herraa1/msx-jio-cart-v1/images/msx-jiocart-v1-flashing-with-wrtsst.png

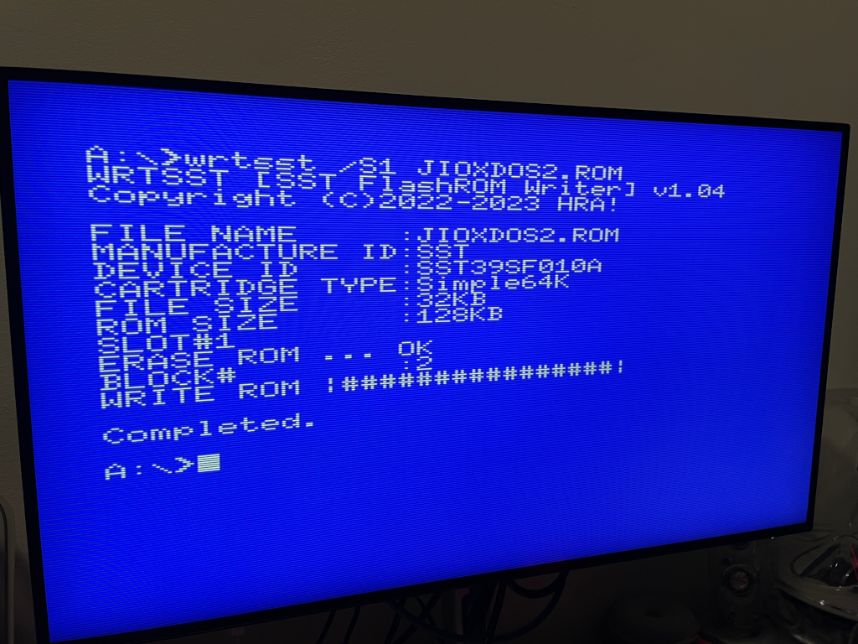
images/msx-jiocart-v1-flashing-with-wrtsst.png
