herraa1/msx-jio-cart-v1/images/msx-jiocart-v1-front-populated-serial-8738.png

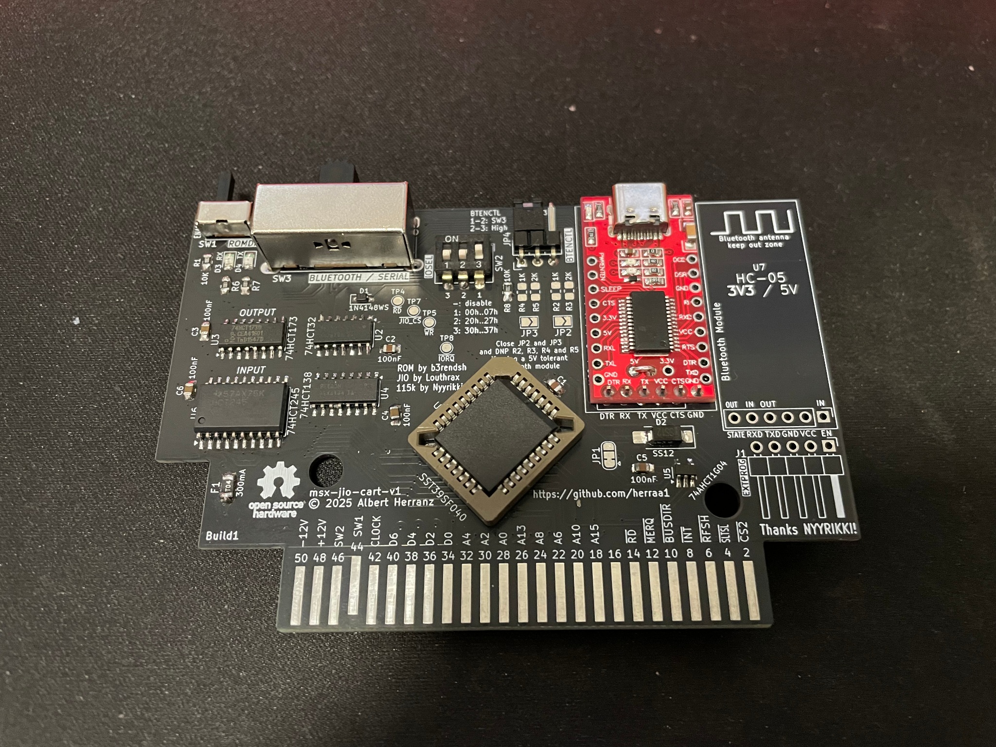
images/msx-jiocart-v1-front-populated-serial-8738.png
